aTinyShellScript/v2.4_AWD/UserMods/xbst_/9mm_Nema_17/STL/OPTIONAL-Tensioner-x2.stl

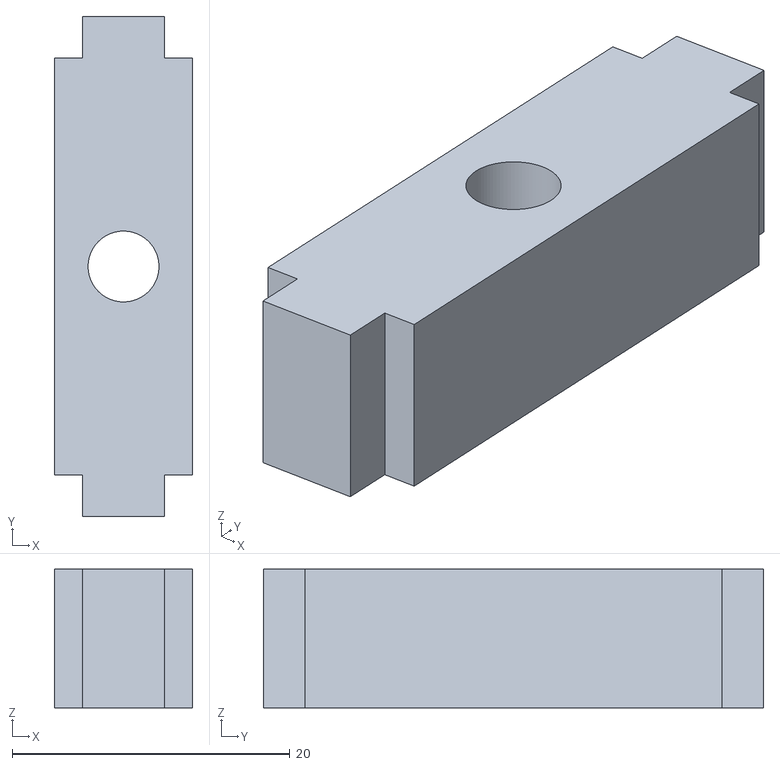
[picture p20: CAD file, 2024-06-21]
UserMods/xbst_/9mm_Nema_17/STL/OPTIONAL-Tensioner-x2.stl
9.94 x 36.0 x 10.0
