aTinyShellScript/v2.4_AWD/DXFs/NEMA14/14_FrontPlate_[x4].dxf

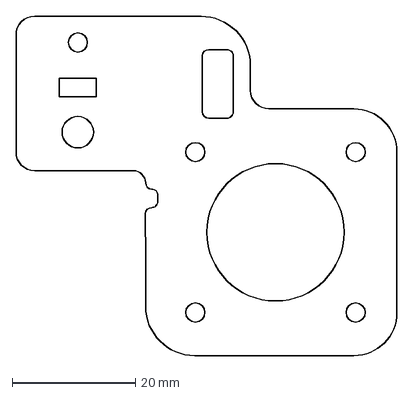
[picture p21: CAD file, 2024-06-21]
DXFs/NEMA14/14_FrontPlate_[x4].dxf
61.8 x 55.0 mm
