aTinyShellScript/v2.4_AWD/DXFs/NEMA14/Alternate/EURO_14_RearPlate_[x4].dxf

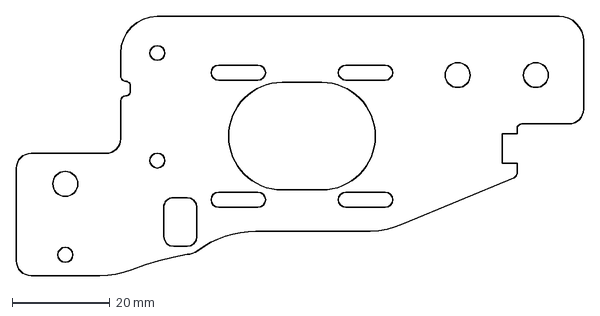
[picture p22: CAD file, 2023-09-11]
DXFs/NEMA14/Alternate/EURO_14_RearPlate_[x4].dxf
116.0 x 53.0 mm
