aTinyShellScript/v2.4_AWD/DXFs/NEMA17/17_RearPlate_[x4].dxf

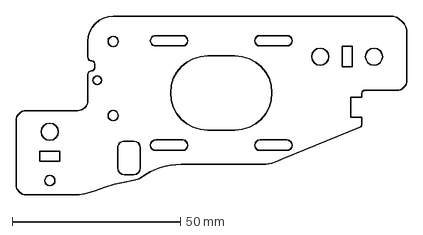
[picture p23: CAD file, 2024-06-21]
DXFs/NEMA17/17_RearPlate_[x4].dxf
116.0 x 53.0 mm
