aTinyShellScript/v2.4_AWD/DXFs/NEMA17/Alternate/EURO_17_RearPlate_[x4].dxf

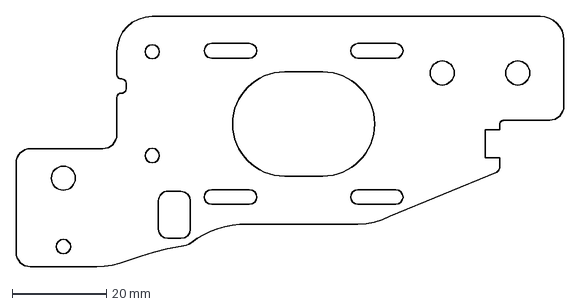
[picture p24: CAD file, 2023-09-11]
DXFs/NEMA17/Alternate/EURO_17_RearPlate_[x4].dxf
116.0 x 53.0 mm
