aTinyShellScript/v2.4_AWD/DXFs/Rear_Plates_[x4].dxf

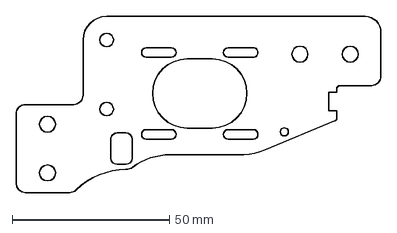
[picture p25: CAD file, 2023-03-08]
DXFs/Rear_Plates_[x4].dxf
116.0 x 56.0 mm
