aTinyShellScript/v2.4_AWD/STLs/NEMA14/MetalPlates/Dual_M5_Aligner_[x4].stl

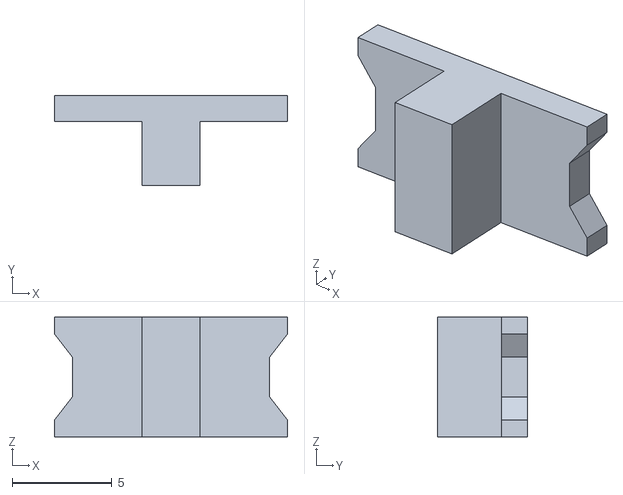
[picture p26: CAD file, 2024-06-21]
STLs/NEMA14/MetalPlates/Dual_M5_Aligner_[x4].stl
11.7 x 4.50 x 6.00
