aTinyShellScript/v2.4_AWD/STLs/NEMA14/Printed/14_Front_Plate_Spacer_Mirrored_[x1].stl

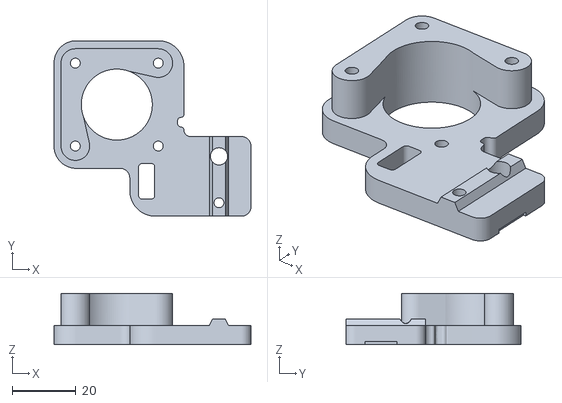
[picture p27: CAD file, 2023-10-12]
STLs/NEMA14/Printed/14_Front_Plate_Spacer_Mirrored_[x1].stl
61.8 x 55.0 x 16.0
