aTinyShellScript/v2.4_AWD/STLs/NEMA14/Printed/SimpleIdlers/SimpleIdler_Spacer_x2.stl

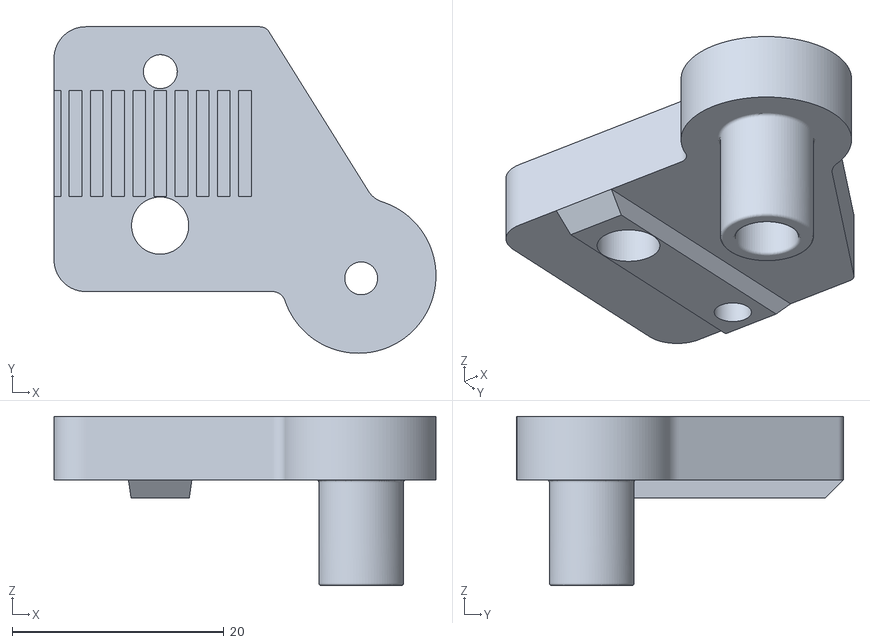
[picture p28: CAD file, 2023-08-28]
STLs/NEMA14/Printed/SimpleIdlers/SimpleIdler_Spacer_x2.stl
36.1 x 30.8 x 16.0
