aTinyShellScript/v2.4_AWD/STLs/NEMA17/MetalPlates/17_FrontMidBody_DoubleT_Pin_Alternate_x2.stl

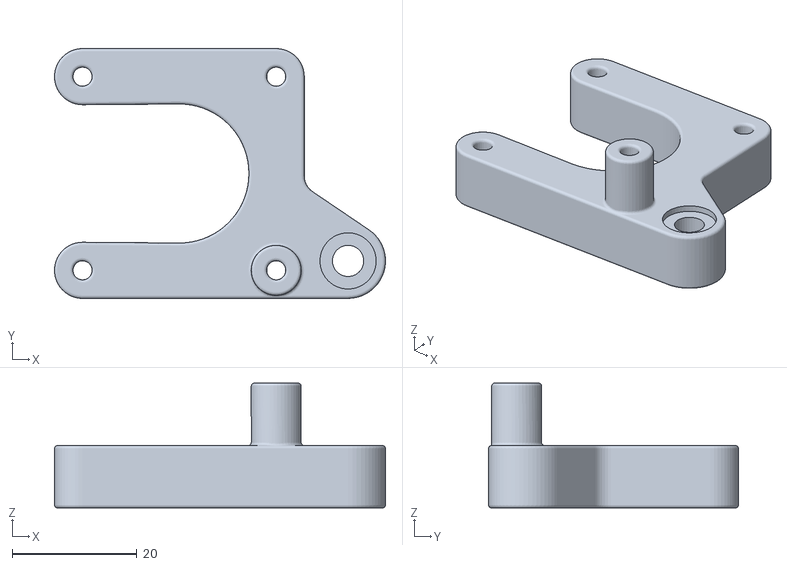
[picture p29: CAD file, 2024-06-21]
STLs/NEMA17/MetalPlates/17_FrontMidBody_DoubleT_Pin_Alternate_x2.stl
53.0 x 40.0 x 20.0
