aTinyShellScript/v2.4_AWD/STLs/NEMA17/MetalPlates/v1 Plates/Rear_Top_Clamp_Grip_[x2].stl

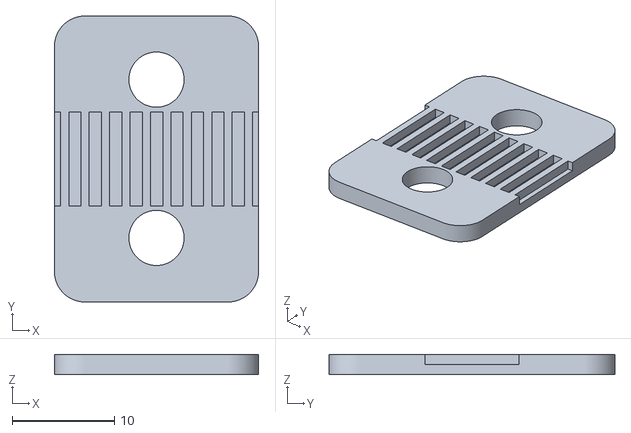
[picture p30: CAD file, 2023-03-20]
STLs/NEMA17/MetalPlates/v1 Plates/Rear_Top_Clamp_Grip_[x2].stl
20.0 x 28.0 x 2.00
