aTinyShellScript/v2.4_AWD/UserMods/xbst_/9mm_Nema_17/STL/Rear-Left-Shaft-Support-x1.stl

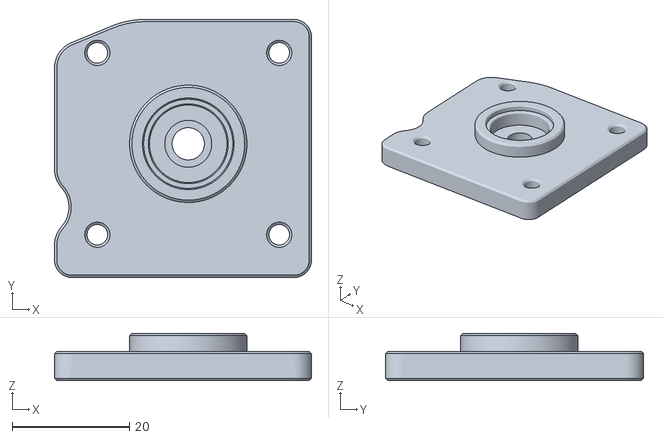
[picture p31: CAD file, 2024-06-21]
UserMods/xbst_/9mm_Nema_17/STL/Rear-Left-Shaft-Support-x1.stl
43.8 x 44.0 x 8.05
