aTinyShellScript/v2.4_AWD/DXFs/Tensioner_Plates_[x2].dxf

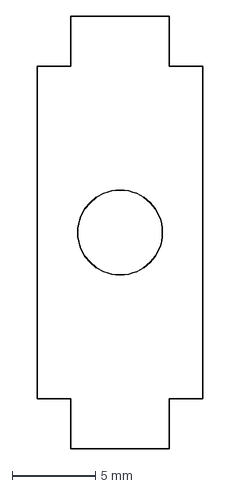
[picture p32: CAD file, 2023-03-08]
DXFs/Tensioner_Plates_[x2].dxf
9.94 x 26.0 mm
