aTinyShellScript/v2.4_AWD/STLs/NEMA14/MetalPlates/v1 Plates/Rear_Bottom_Clamp_[x2].stl

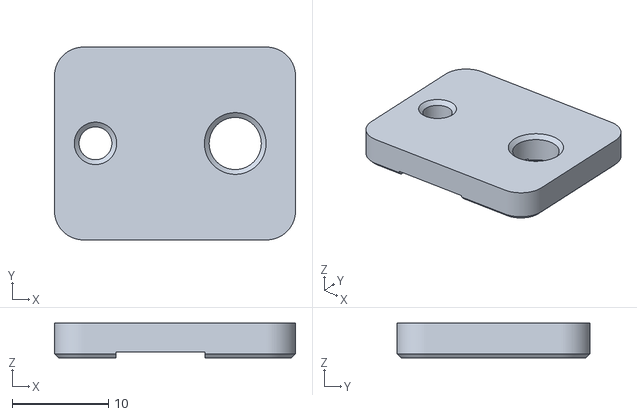
[picture p34: CAD file, 2023-03-20]
STLs/NEMA14/MetalPlates/v1 Plates/Rear_Bottom_Clamp_[x2].stl
25.0 x 20.0 x 3.60
