aTinyShellScript/v2.4_AWD/STLs/NEMA17/Printed/17_TensionerPlate_x2.stl

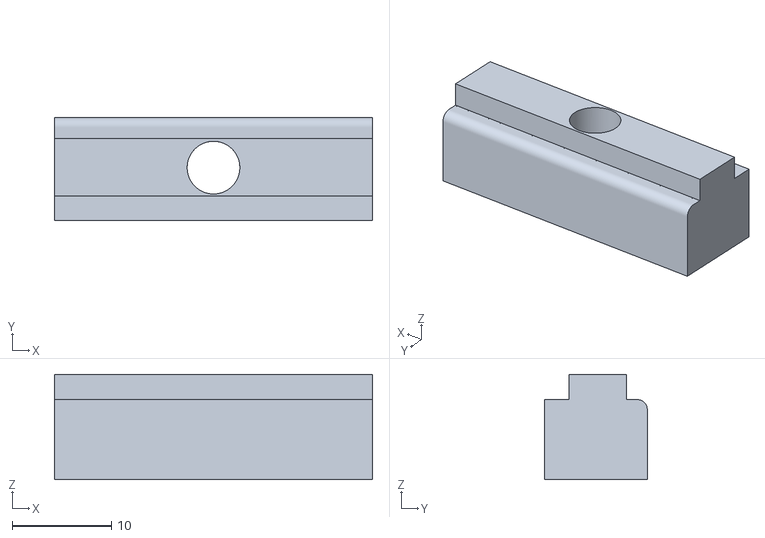
[picture p35: CAD file, 2023-05-05]
STLs/NEMA17/Printed/17_TensionerPlate_x2.stl
32.0 x 10.3 x 10.6
