aTinyShellScript/v2.4_AWD/UserMods/xbst_/9mm_Nema_17/STL/Rear-Motor-Spacer-x2.stl

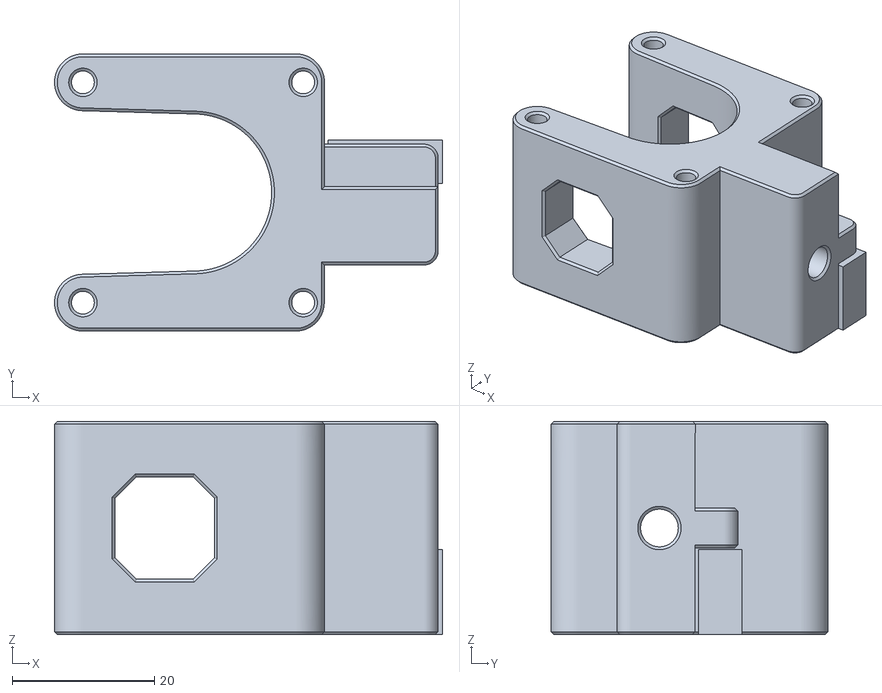
[picture p36: CAD file, 2024-06-21]
UserMods/xbst_/9mm_Nema_17/STL/Rear-Motor-Spacer-x2.stl
54.6 x 39.0 x 30.0
