aTinyShellScript/v2.4_AWD/STLs/NEMA14/MetalPlates/14_FrontMidBody_[x2].stl

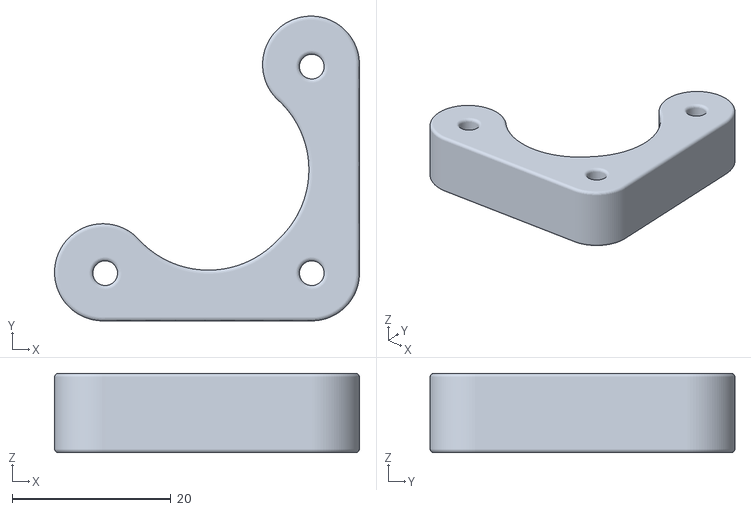
[picture p37: CAD file, 2023-08-29]
STLs/NEMA14/MetalPlates/14_FrontMidBody_[x2].stl
38.4 x 38.4 x 10.0
