aTinyShellScript/v2.4_AWD/STLs/NEMA14/Printed/14_Front_Plate_Mirrored_[x1].stl

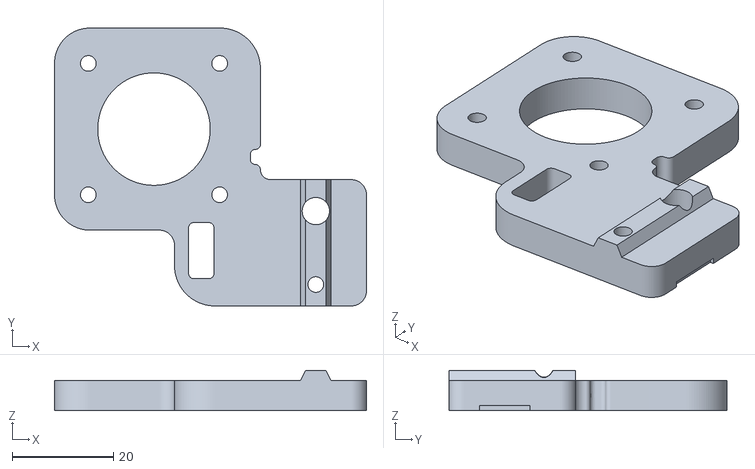
[picture p38: CAD file, 2023-10-12]
STLs/NEMA14/Printed/14_Front_Plate_Mirrored_[x1].stl
61.7 x 55.0 x 8.00
