aTinyShellScript/v2.4_AWD/UserMods/xbst_/9mm_Nema_17/STL/Front-Motor-Spacer-x2.stl

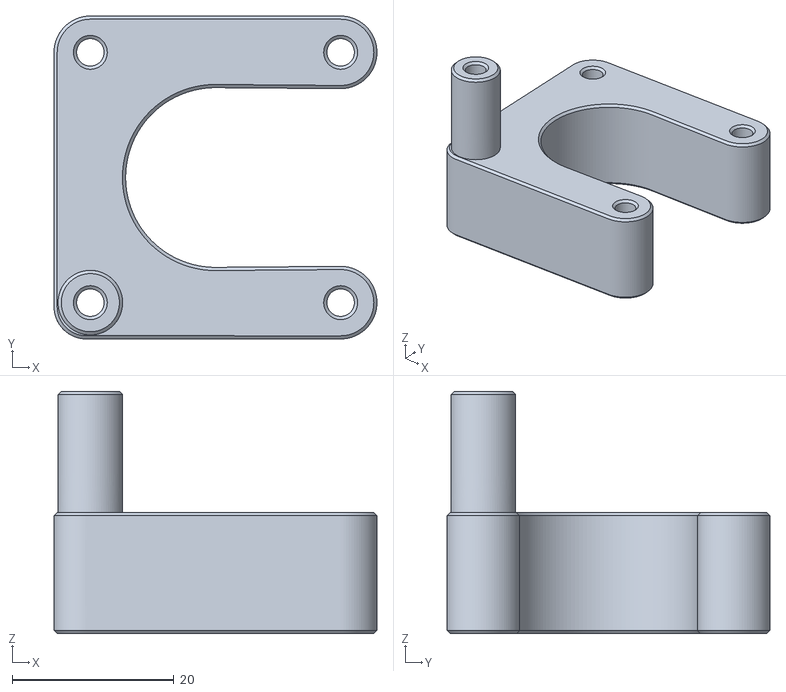
[picture p39: CAD file, 2024-06-21]
UserMods/xbst_/9mm_Nema_17/STL/Front-Motor-Spacer-x2.stl
40.0 x 40.0 x 30.0
