aTinyShellScript/v2.4_AWD/STLs/NEMA14/MetalPlates/10mmSpacer_[x2].stl

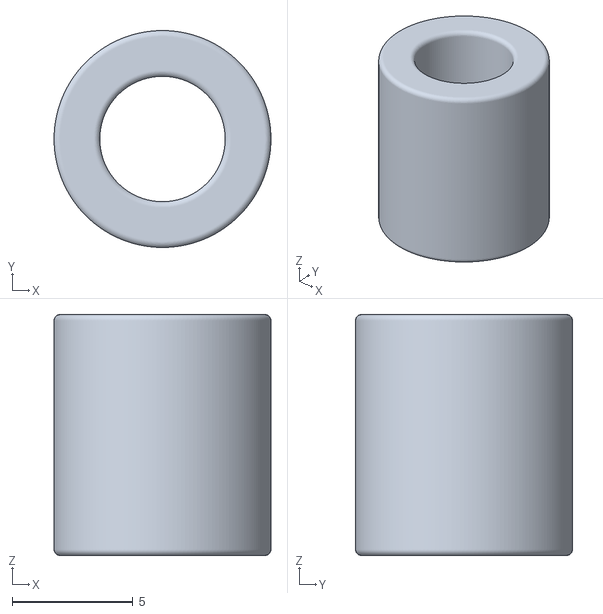
[picture p40: CAD file, 2023-07-05]
STLs/NEMA14/MetalPlates/10mmSpacer_[x2].stl
9.00 x 9.00 x 10.0
