aTinyShellScript/v2.4_AWD/STLs/NEMA17/Printed/17_FrontPlateSpacer_x2.stl

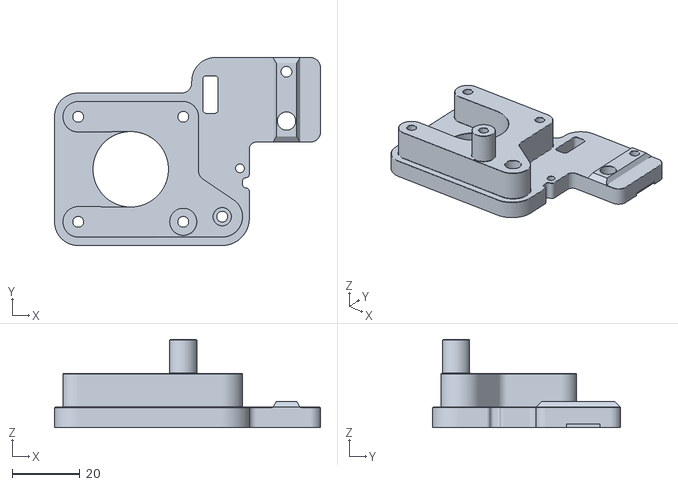
[picture p41: CAD file, 2023-05-05]
STLs/NEMA17/Printed/17_FrontPlateSpacer_x2.stl
78.5 x 55.5 x 26.0
