aTinyShellScript/v2.4_AWD/STLs/NEMA17/Printed/17_RearUpperPlate_A_x1.stl

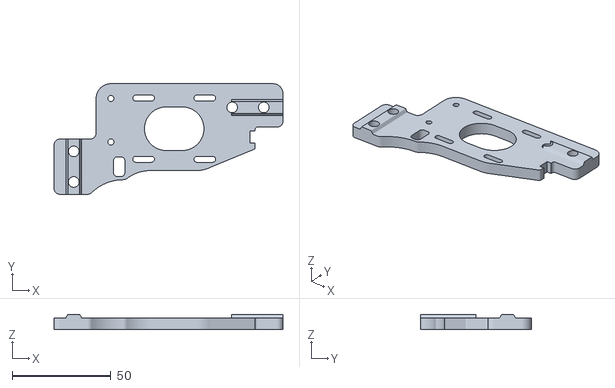
[picture p42: CAD file, 2023-05-05]
STLs/NEMA17/Printed/17_RearUpperPlate_A_x1.stl
116.0 x 56.0 x 7.70
