aTinyShellScript/v2.4_AWD/STLs/NEMA14/Printed/14_RearTensioners_Supported_[x2].stl

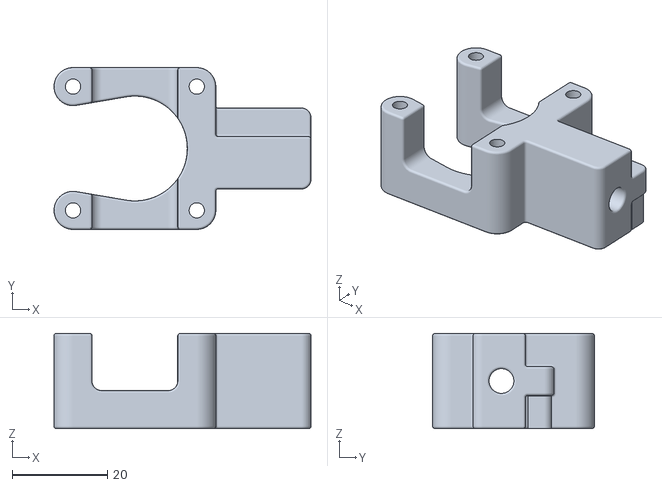
[picture p43: CAD file, 2023-09-15]
STLs/NEMA14/Printed/14_RearTensioners_Supported_[x2].stl
54.0 x 34.0 x 20.0
