aTinyShellScript/v2.4_AWD/UserMods/xbst_/9mm_Nema_17/STL/Rear-Extrusion-Spacer-x4.stl

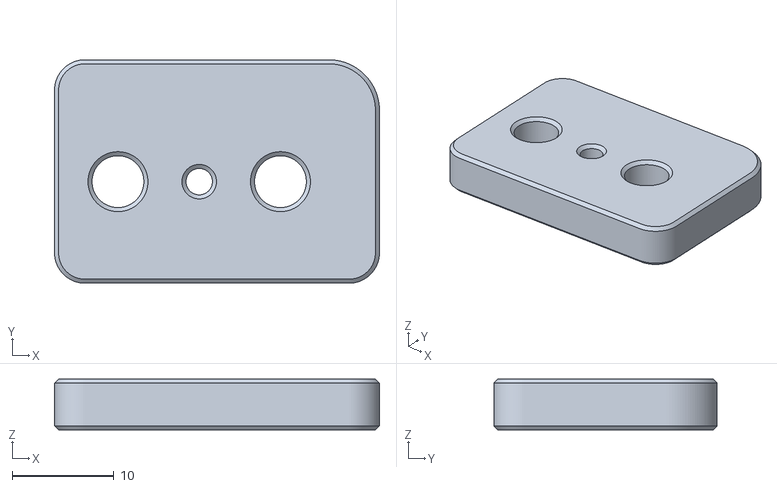
[picture p44: CAD file, 2024-06-21]
UserMods/xbst_/9mm_Nema_17/STL/Rear-Extrusion-Spacer-x4.stl
32.0 x 22.0 x 5.00
