aTinyShellScript/v2.4_AWD/STLs/NEMA17/Printed/17_FrontPlate_x2.stl

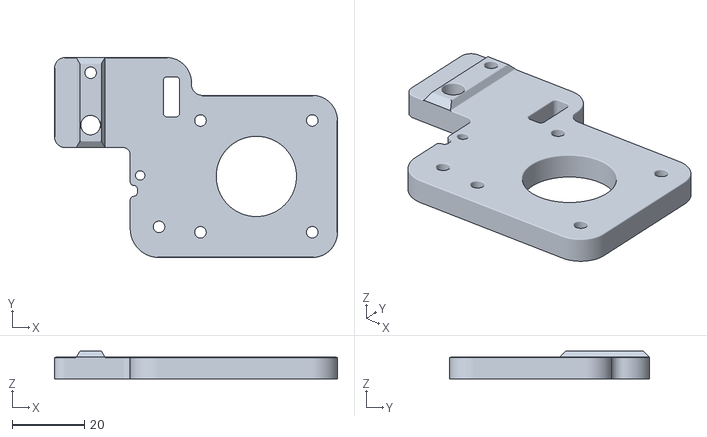
[picture p45: CAD file, 2023-05-04]
STLs/NEMA17/Printed/17_FrontPlate_x2.stl
78.5 x 55.5 x 7.70
