aTinyShellScript/v2.4_AWD/UserMods/xbst_/9mm_Nema_17/STL/Side-Extrusion-Spacer-x8.stl

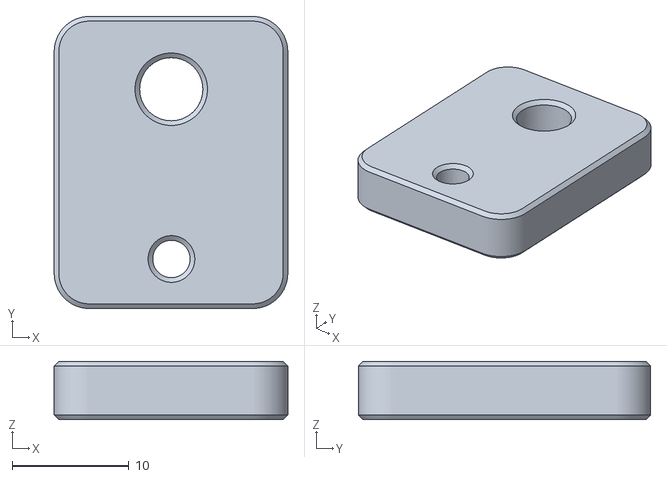
[picture p48: CAD file, 2024-06-21]
UserMods/xbst_/9mm_Nema_17/STL/Side-Extrusion-Spacer-x8.stl
20.0 x 25.0 x 5.00
