aTinyShellScript/v2.4_AWD/UserMods/xbst_/9mm_Nema_17/STL/Front-Right-Shaft-Support-x1.stl

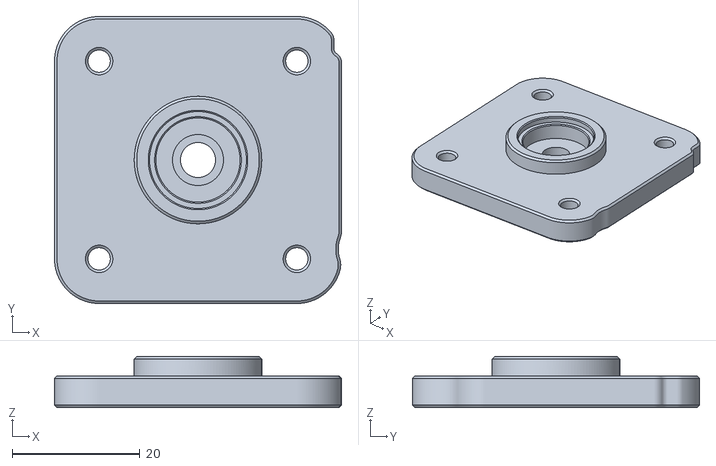
[picture p49: CAD file, 2024-06-21]
UserMods/xbst_/9mm_Nema_17/STL/Front-Right-Shaft-Support-x1.stl
45.0 x 45.0 x 8.05
